T-622/uDR1399-10V-Reference-Standard/uDR1399 Validation Tests/5min Tests/100PLC/100PLC_05.JPG

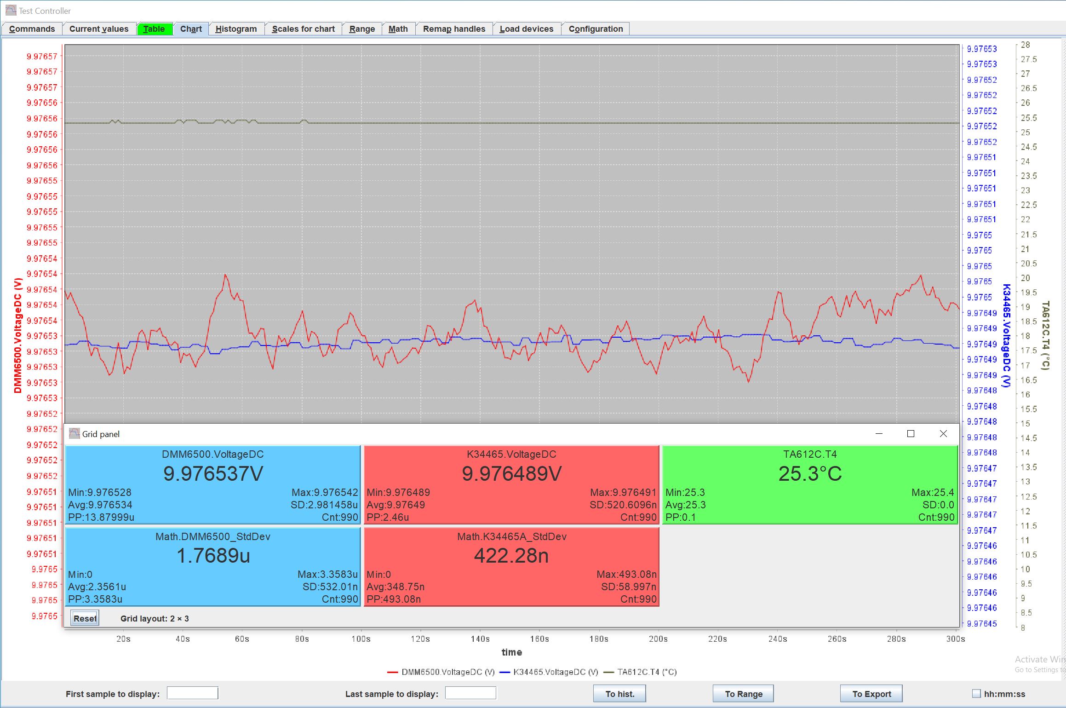
uDR1399 Validation Tests/5min Tests/100PLC/100PLC_05.JPG
