T-622/uDR1399-10V-Reference-Standard/uDR1399 Validation Tests/10min Tests/10PLC + 10x Smoothing/10PLC_With_Filter_02.JPG

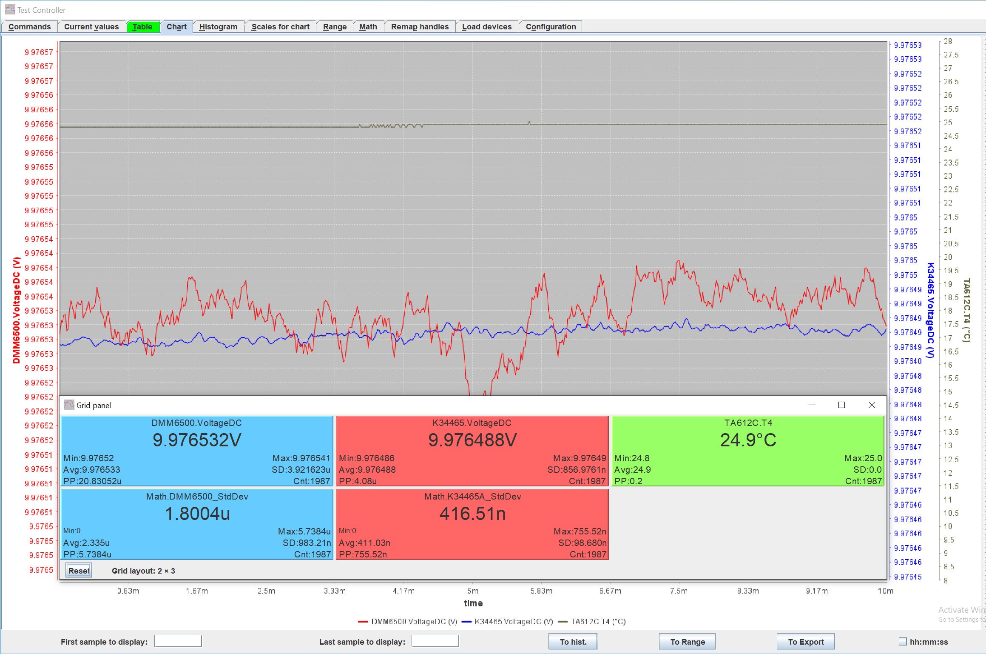
uDR1399 Validation Tests/10min Tests/10PLC + 10x Smoothing/10PLC_With_Filter_02.JPG
